vphilippoz/pharmacy/Software/animation_library/fortnite_animation.gif

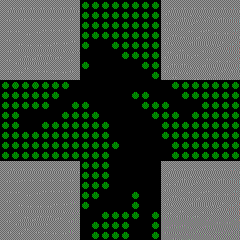
Software/animation_library/fortnite_animation.gif
