vphilippoz/pharmacy/Software/animation_library/girl_animation.gif

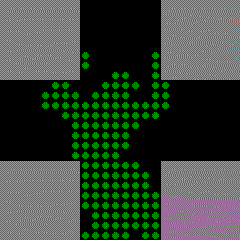
Software/animation_library/girl_animation.gif
