vphilippoz/pharmacy/Software/src/peripherals/peripherals.ino

/*
Minimal version to test the module.

This code is a minimal version to test the module. It toggles the defined GPIOs and the corresponding LED color.
*/

#include "peripherals.hpp"

// Constants
constexpr unsigned int SERIAL_BAUD_RATE = 115200;
constexpr bool VERBOSE = false;


void setup() {
    if(VERBOSE) {
        // Open serial communications on the native USB port
        Serial.begin(SERIAL_BAUD_RATE);while(!Serial);
    }

    // Setup the library
    peripherals::setup(VERBOSE);
    if(VERBOSE) {Serial.println("Setup complete");}
}

void loop() {
    // Declare variables
    static uint8_t brightness = 0;
    static std::vector<std::vector<uint16_t>> frame = {
        {0x0000, 0x0000, 0x7E40, 0x087F, 0x0E42, 0x0004, 0x0000, 0x0000}, // Top panel
        {0x0000, 0x0000, 0x2424, 0x542A, 0x5432, 0x5C24, 0x0000, 0x0000}, // Bottom panel
        {0x0000, 0x0000, 0x006C, 0x0092, 0x0092, 0x0044, 0x0000, 0x0000}, // Center panel
    };
    static bool change_anim = false;
    static uint16_t speed = 200; // [ms]
    
    // Get user inputs
    change_anim = peripherals::get_next_animation_required();
    uint8_t tmp_brightness = peripherals::get_brightness();
    speed = peripherals::get_speed();

    // Update brightness if it has changed
    if(tmp_brightness != brightness) {
        brightness = tmp_brightness;
        peripherals::set_brightness(brightness);
    }

    // Update the LED matrices
    peripherals::set_frame(frame);

    // Print infos
    if(VERBOSE) {
        Serial.print("Brightness: ");
        Serial.println(tmp_brightness);
        Serial.print("Next animation required: ");
        Serial.println(change_anim ? "Yes" : "No");
        Serial.print("Animation speed: ");
        Serial.println(speed);
    }
    
    // Invert the frame for the next loop
    for (size_t i = 0; i < frame.size(); i++) {
        for (size_t j = 0; j < frame[i].size(); j++) {
            frame[i][j] = ~frame[i][j]; // Invert the bits to create a new pattern
        }
    }

    // Delay before the next update
    delay(speed); // [ms]
}
